acwright/6502-ACE/Models/CherryMX.step

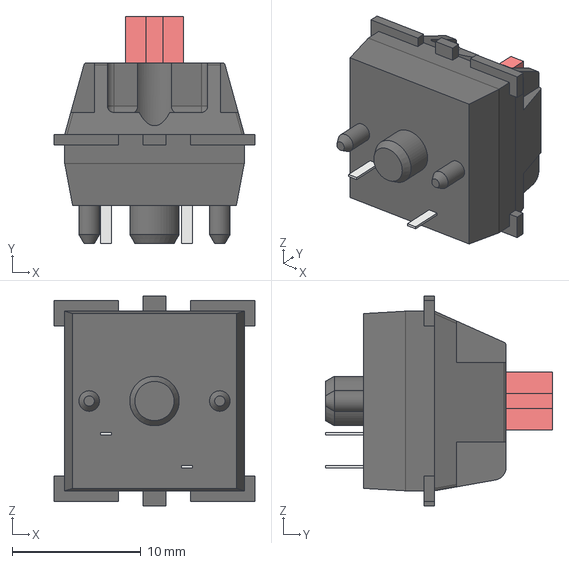
[picture p20: CAD file, 2026-04-29]
Models/CherryMX.step
15.6 x 17.7 x 16.3 mm
