acwright/6502-ACE/Models/228-1277-00-0602J.step

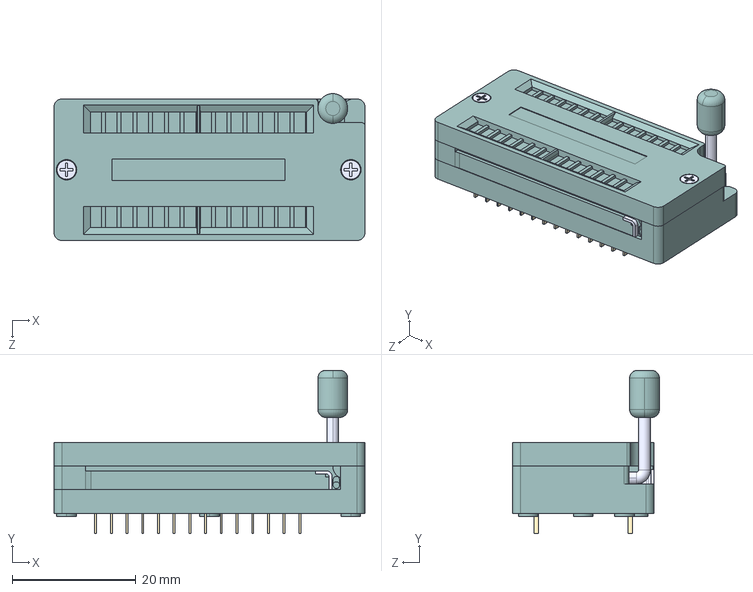
[picture p21: CAD file, 2026-04-29]
Models/228-1277-00-0602J.step
50.3 x 26.4 x 23.7 mm
