acwright/6502-ACE/Models/5-5530843-4.step

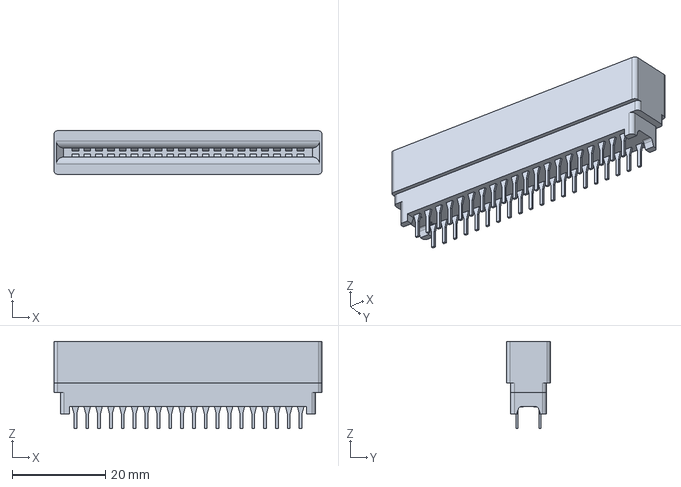
[picture p22: CAD file, 2026-04-29]
Models/5-5530843-4.step
57.4 x 9.35 x 18.7 mm
