acwright/6502-ACE/Models/BAT-HLD-001-THM.step

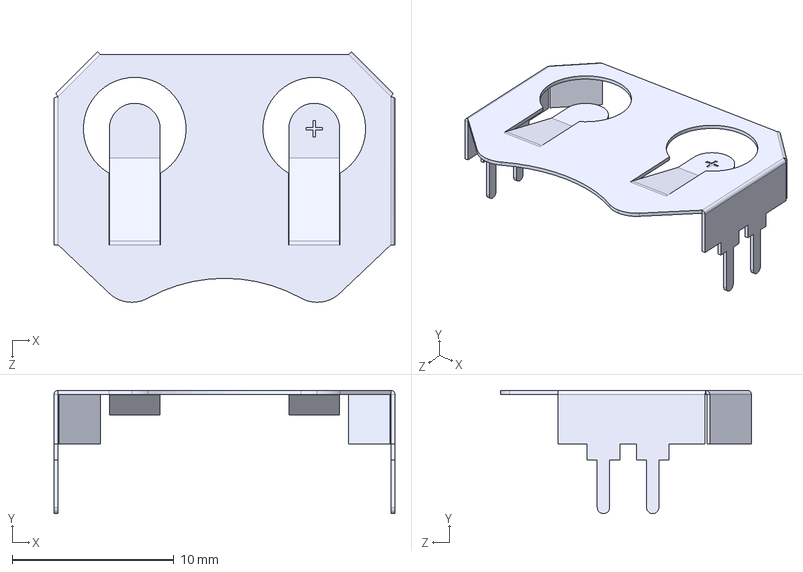
[picture p23: CAD file, 2026-04-29]
Models/BAT-HLD-001-THM.step
21.1 x 7.62 x 15.5 mm
